Escrich/00-Camion_Share_Horizons_version_Escrich-00/Imagenes/IMG20250401224726.jpg

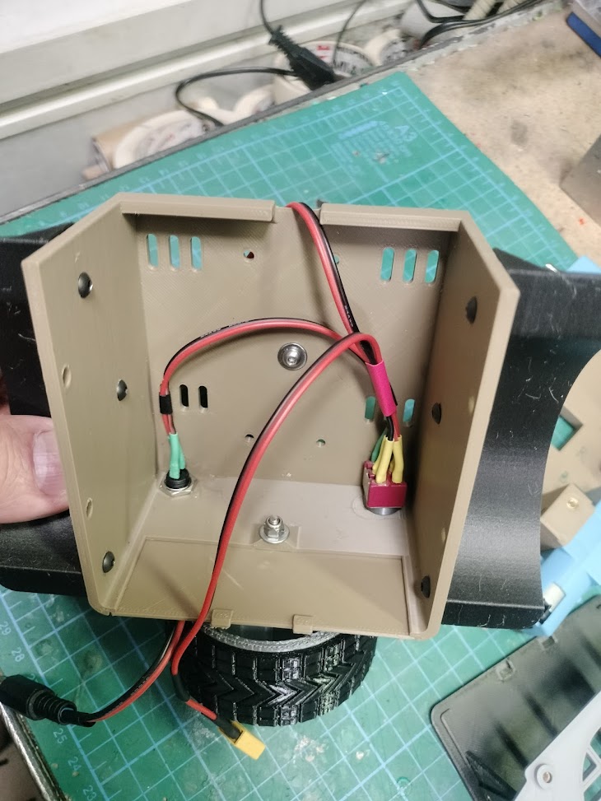
Imagenes/IMG20250401224726.jpg
