Escrich/00-Camion_Share_Horizons_version_Escrich-00/Imagenes/IMG20250403135836.jpg

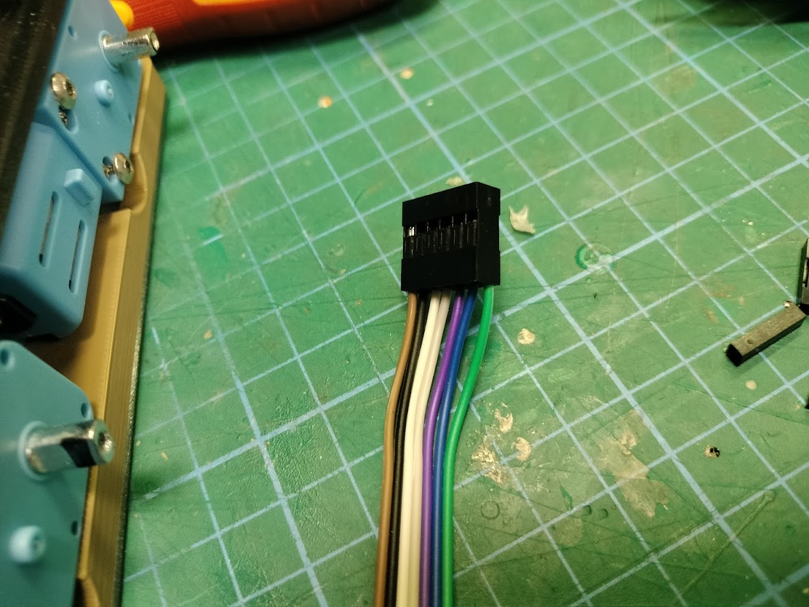
Imagenes/IMG20250403135836.jpg
