Escrich/00-Camion_Share_Horizons_version_Escrich-00/Imagenes/IMG20250403173520.jpg

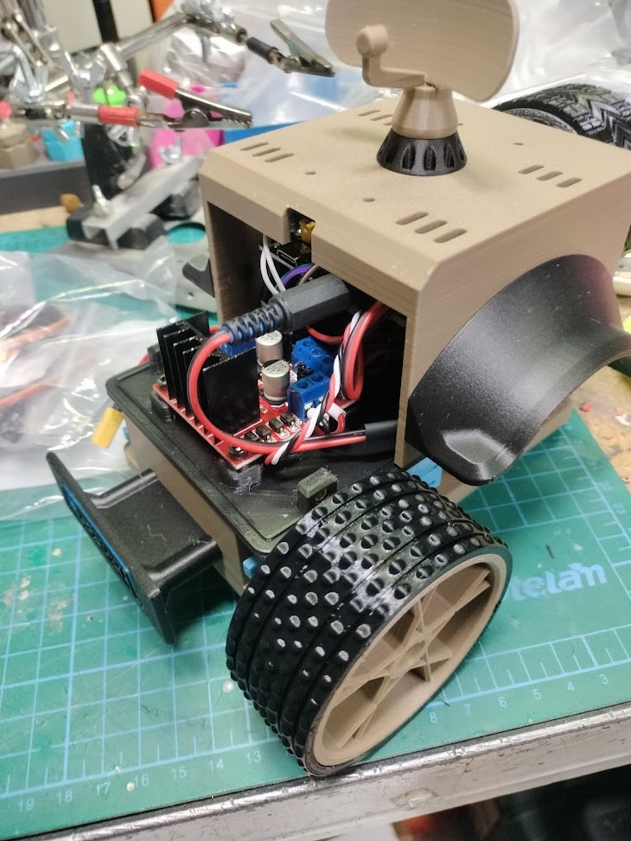
Imagenes/IMG20250403173520.jpg
