Escrich/00-Camion_Share_Horizons_version_Escrich-00/Imagenes/IMG20250403194223.jpg

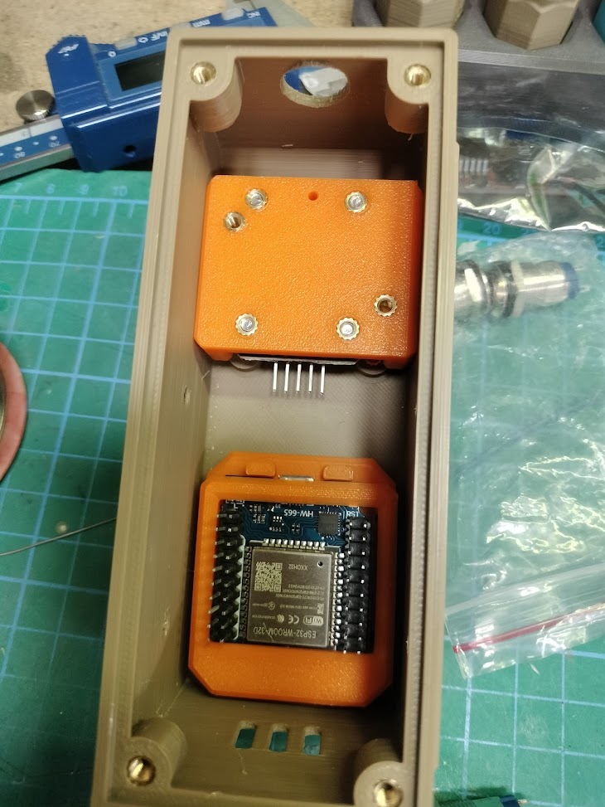
Imagenes/IMG20250403194223.jpg
