Escrich/00-Camion_Share_Horizons_version_Escrich-00/Accesorios ruedas amarillas/Ruedas amarillas OBJ o STL/20250314 Camión Share Horizons-tapacubos.obj

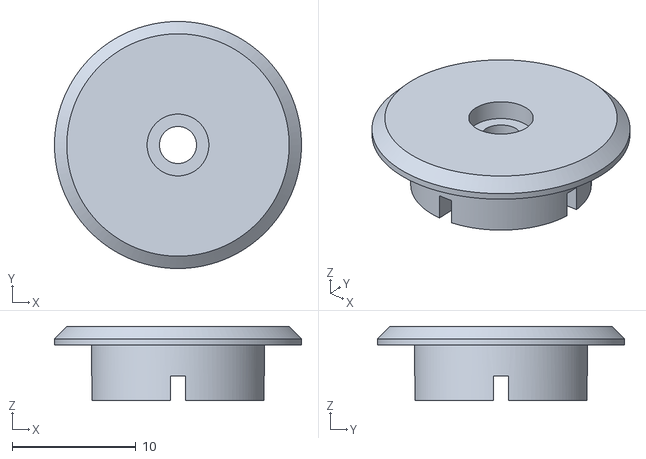
[picture p84: CAD file, 2025-06-03]
Accesorios ruedas amarillas/Ruedas amarillas OBJ o STL/20250314 Camión Share Horizons-tapacubos.obj
20.0 x 20.0 x 6.00
