Escrich/00-Camion_Share_Horizons_version_Escrich-00/Brazos/Brazos OBJ o STL/20250316 Camion - reformas - brazo con falsos tornillos.obj

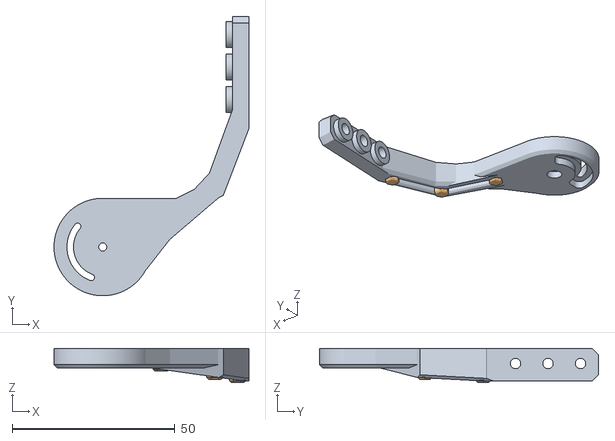
[picture p85: CAD file, 2025-06-03]
Brazos/Brazos OBJ o STL/20250316 Camion - reformas - brazo con falsos tornillos.obj
60.0 x 86.0 x 10.5
brazo nuevo con dibujo corredera opuesta
simulacion tornillos en brazo
