Escrich/00-Camion_Share_Horizons_version_Escrich-00/Mando a distancia/Mando OBJ o STL/20250321 Mando a distancia camioncito-tapa mando.obj

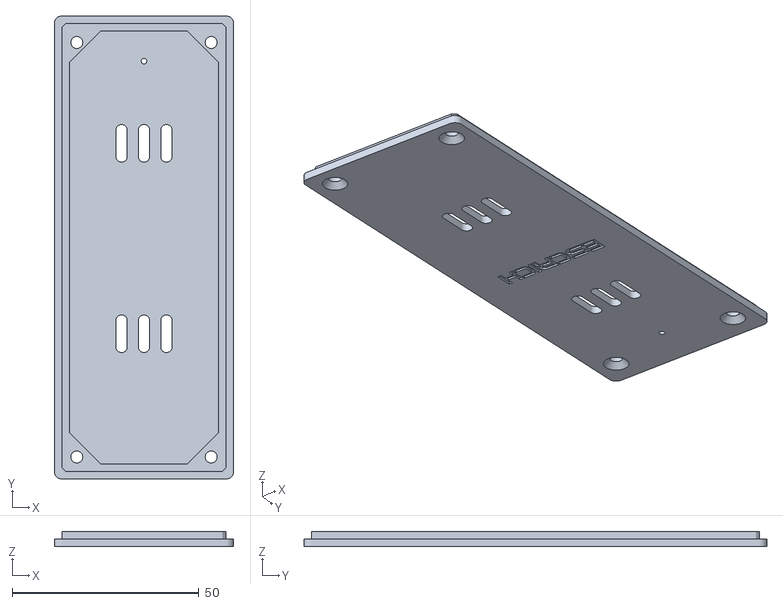
[picture p86: CAD file, 2025-06-03]
Mando a distancia/Mando OBJ o STL/20250321 Mando a distancia camioncito-tapa mando.obj
48.0 x 124.0 x 4.00
